slesinger/volume-control/volctrl/custom_components/vol_ctrl/background.h

#pragma once
#include <cstdint>
#include <pgmspace.h>
// 240x240 RGB565 default background (generated from the supplied picture)
static const uint16_t BACKGROUND_IMAGE[240 * 240] PROGMEM = {
0x0024,0x0024,0x0024,0x0024,0x0024,0x0024,0x0024,0x0024,0x0024,0x0024,0x0024,0x0024,0x0024,0x0025,0x0025,0x0025,
0x0025,0x0025,0x0025,0x0025,0x0025,0x0025,0x0025,0x0025,0x0025,0x0025,0x0025,0x0025,0x0025,0x0045,0x0045,0x0045,
0x0045,0x0045,0x0045,0x0045,0x0045,0x0045,0x0045,0x0045,0x0045,0x0045,0x0045,0x0045,0x0045,0x0045,0x0045,0x0045,
0x0045,0x0045,0x0045,0x0045,0x0045,0x0045,0x0045,0x0045,0x0045,0x0045,0x0045,0x0045,0x0045,0x0045,0x0045,0x0045,
0x0045,0x0045,0x0045,0x0045,0x0045,0x0045,0x0045,0x0045,0x0045,0x0045,0x0045,0x0045,0x0045,0x0045,0x0045,0x0045,
0x0045,0x0045,0x0045,0x0045,0x0045,0x0045,0x0045,0x0045,0x0045,0x0045,0x0045,0x0045,0x0045,0x0045,0x0045,0x0045,
0x0045,0x0045,0x0045,0x0045,0x0045,0x0045,0x0045,0x0045,0x0045,0x0045,0x0045,0x0045,0x0045,0x0045,0x0045,0x0045,
0x0045,0x0045,0x0045,0x0045,0x0045,0x0045,0x0045,0x0045,0x0025,0x0025,0x0025,0x0025,0x0025,0x0025,0x0025,0x0025,
0x0025,0x0025,0x0025,0x0025,0x0025,0x0024,0x0024,0x0024,0x0025,0x0025,0x0024,0x0024,0x0024,0x0024,0x0024,0x0024,
0x0024,0x0024,0x0024,0x0024,0x0024,0x0024,0x0024,0x0024,0x0024,0x0024,0x0024,0x0024,0x0024,0x0024,0x0024,0x0024,
0x0024,0x0004,0x0004,0x0004,0x0004,0x0004,0x0004,0x0004,0x0004,0x0004,0x0004,0x0004,0x0004,0x0004,0x0004,0x0004,
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
0x0025,0x0025,0x0025,0x0025,0x0025,0x0024,0x0024,0x0024,0x0025,0x0025,0x0025,0x0025,0x0025,0x0025,0x0025,0x0025,
0x0024,0x0024,0x0024,0x0024,0x0024,0x0024,0x0024,0x0024,0x0024,0x0024,0x0024,0x0024,0x0024,0x0024,0x0024,0x0024,
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
};
