slesinger/volume-control/volctrl/custom_components/vol_ctrl/volume_font.h

#pragma once
// Orbitron (SIL Open Font License) digits rendered to Adafruit-GFX format by a script; chars 0x2D..0x39
#include <pgmspace.h>
#include <TFT_eSPI.h>  // brings in GFXfont
static const uint8_t OrbitronDigitsBitmaps[] PROGMEM = {
0x7F,0xFF,0xFF,0xFF,0xFB,0xFF,0xFF,0xFF,0xFF,0xFF,0xFF,0xFF,0xFF,0xFF,0xFF,0xFF,0xFF,0xFF,0xFF,0xFF,0xFF,0xFF,0xFF,0xFF,0xFF,0xFF,0xFF,0xFF,0xFF,0xFF,0xFF,0xFF,0xFF,0xFF,0xFF,0xFF,0xFF,0xFF,0xFF,0xFF,0xFF,0xFF,0xFF,0xFF,0xFF,0xFF,0xFF,0xFF,0xFF,0xFF,0xFF,0xFF,0xC0,0xFF,0xFF,0xFF,0xFF,0xFF,0xFF,0xFF,0xFF,0xFF,0xFF,0xFF,0xFF,0xFF,0xFF,0xFF,0x80,0x00,0x00,0x00,0x00,0x00,0x1E,0x00,0x00,0x00,0x00,0x00,0x7C,0x00,0x00,0x00,0x00,0x00,0xF8,0x00,0x00,0x00,0x00,0x03,0xF0,0x00,0x00,0x00,0x00,0x0F,0xE0,0x00,0x00,0x00,0x00,0x3F,0xC0,0x00,0x00,0x00,0x00,0xFF,0x80,0x00,0x00,0x00,0x01,0xFF,0x00,0x00,0x00,0x00,0x07,0xFE,0x00,0x00,0x00,0x00,0x1F,0xFC,0x00,0x00,0x00,0x00,0x7F,0xF8,0x00,0x00,0x00,0x01,0xFF,0xF0,0x00,0x00,0x00,0x07,0xFF,0xC0,0x00,0x00,0x00,0x0F,0xFF,0x00,0x00,0x00,0x00,0x3F,0xFC,0x00,0x00,0x00,0x00,0xFF,0xF8,0x00,0x00,0x00,0x03,0xFF,0xE0,0x00,0x00,0x00,0x0F,0xFF,0x80,0x00,0x00,0x00,0x1F,0xFE,0x00,0x00,0x00,0x00,0x7F,0xF8,0x00,0x00,0x00,0x01,0xFF,0xE0,0x00,0x00,0x00,0x07,0xFF,0xC0,0x00,0x00,0x00,0x1F,0xFF,0x00,0x00,0x00,0x00,0x7F,0xFC,0x00,0x00,0x00,0x00,0xFF,0xF0,0x00,0x00,0x00,0x03,0xFF,0xC0,0x00,0x00,0x00,0x0F,0xFF,0x80,0x00,0x00,0x00,0x3F,0xFE,0x00,0x00,0x00,0x00,0xFF,0xF8,0x00,0x00,0x00,0x01,0xFF,0xE0,0x00,0x00,0x00,0x07,0xFF,0x80,0x00,0x00,0x00,0x1F,0xFE,0x00,0x00,0x00,0x00,0x7F,0xFC,0x00,0x00,0x00,0x01,0xFF,0xF0,0x00,0x00,0x00,0x07,0xFF,0xC0,0x00,0x00,0x00,0x0F,0xFF,0x00,0x00,0x00,0x00,0x3F,0xFC,0x00,0x00,0x00,0x00,0xFF,0xF8,0x00,0x00,0x00,0x03,0xFF,0xE0,0x00,0x00,0x00,0x0F,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
0x00,0x7F,0xF0,0x00,0x00,0x00,0x00,0x00,0x00,0x3F,0xFF,0xFF,0xFF,0xFF,0xFF,0xFF,0xFF,0xFF,0xFF,0xFF,0xFF,0xFF,0xFF,0xFF,0xFF,0xFF,0xFF,0x9F,0xFF,0xFF,0xFF,0xFF,0xFF,0xFF,0xFF,0xE7,0xFF,0xFF,0xFF,0xFF,0xFF,0xFF,0xFF,0xF8,0xFF,0xFF,0xFF,0xFF,0xFF,0xFF,0xFF,0xFC,0x3F,0xFF,0xFF,0xFF,0xFF,0xFF,0xFF,0xFF,0x07,0xFF,0xFF,0xFF,0xFF,0xFF,0xFF,0xFF,0x80,0xFF,0xFF,0xFF,0xFF,0xFF,0xFF,0xFF,0xC0,0x1F,0xFF,0xFF,0xFF,0xFF,0xFF,0xFF,0xE0,0x01,0xFF,0xFF,0xFF,0xFF,0xFF,0xFF,0xE0,0x00,0x1F,0xFF,0xFF,0xFF,0xFF,0xFF,0xE0,0x00};
static const GFXglyph OrbitronDigitsGlyphs[] PROGMEM = {
{0,38,11,48,5,-33},
{53,11,11,21,5,-11},
{69,47,66,48,1,-66},
{457,66,66,77,5,-66},
{1002,31,66,36,1,-66},
{1258,66,66,76,5,-66},
{1803,66,66,76,5,-66},
{2348,63,66,67,1,-66},
{2868,66,66,76,5,-66},
{3413,66,66,75,5,-66},
{3958,55,66,61,0,-66},
{4412,66,66,77,5,-66},
{4957,66,66,76,5,-66}};
static const GFXfont OrbitronDigits PROGMEM = {(uint8_t *)OrbitronDigitsBitmaps, (GFXglyph *)OrbitronDigitsGlyphs, 0x2D, 0x39, 117};
